jennifer1i/longhorn-neon-sign/Images/IMG_8699.png

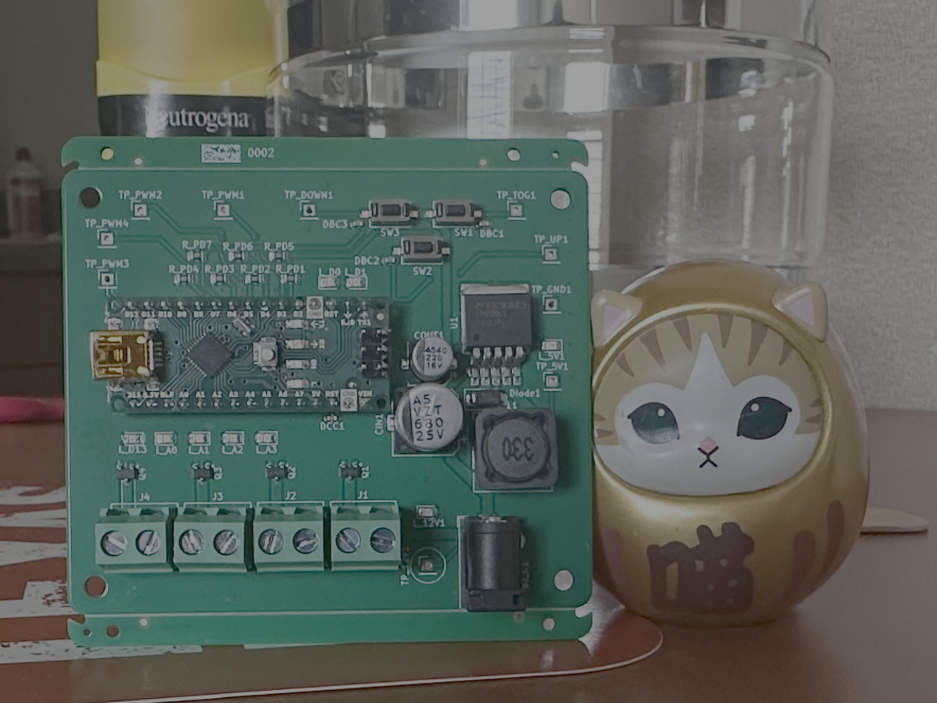
Images/IMG_8699.png
